dennis9819/Z8C-Homebrew-Computer/Modules/001-CPU Board V1/Schematics.pdf

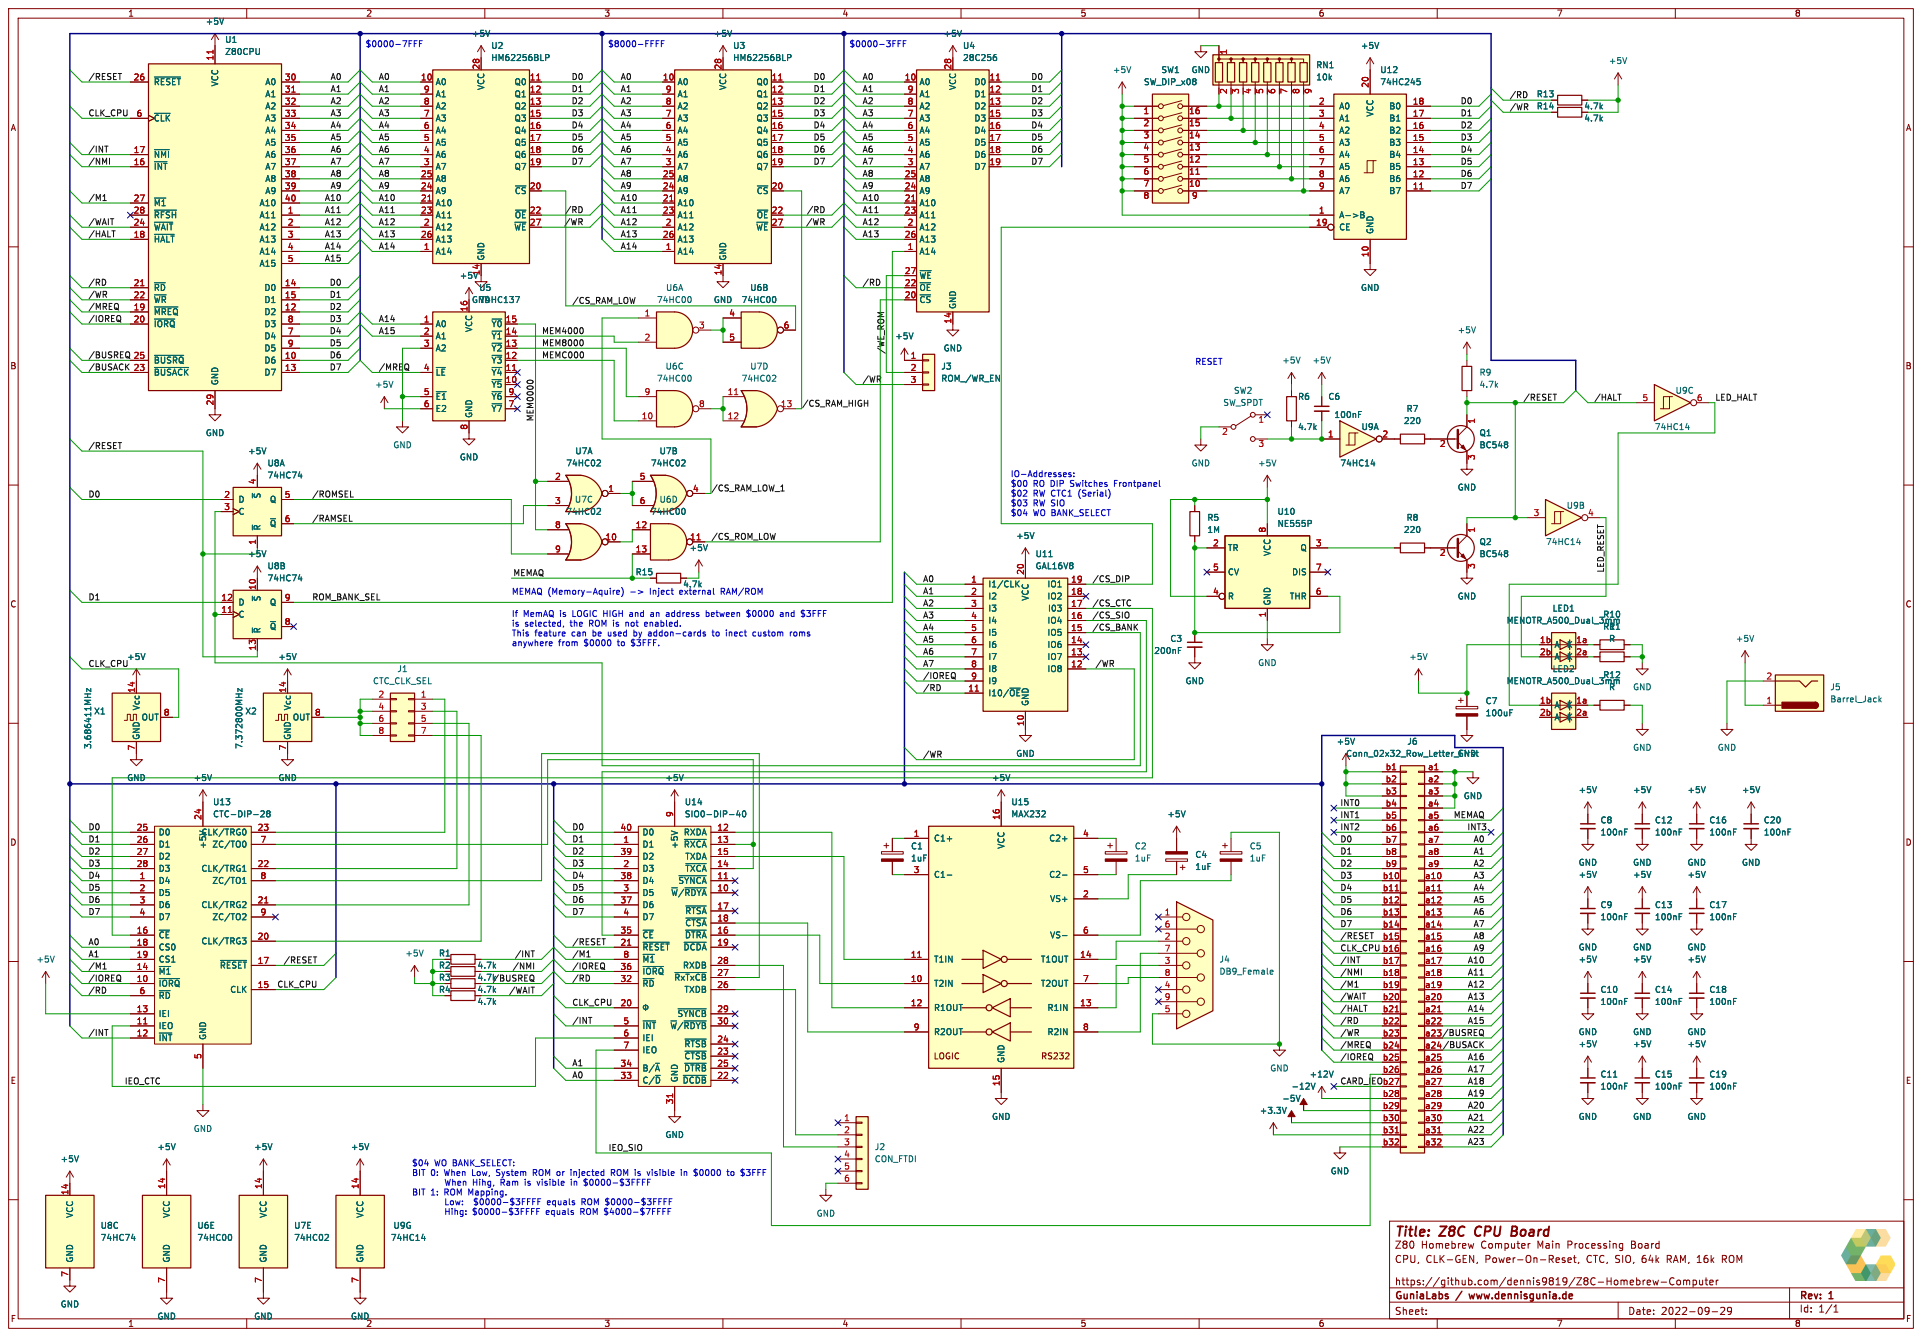
[picture p10: page 1]

IO-Addresses: $00 RO DIP Switches Frontpanel $02 RW CTC1 (Serial) $03 RW SIO
+5V U11 GAL16V8 GND 10 VCC 20

If MemAQ is LOGIC HIGH and an address between $0000 and $3FFF

5 ~{RD} 6 ZC/TO0 7 ZC/TO1 8 ZC/TO2 9 GND +5V

5 ~{RD} 6 ZC/TO0 7 ZC/TO1 8 ZC/TO2 9 U13 CTC-DIP-28 GND

Id: 1/1 Title: Z8C CPU Board

https://github.com/dennis9819/Z8C-Homebrew-Computer
