dennis9819/Z8C-Homebrew-Computer/Modules/002-MIO Board V1/Schematics_Rev2.pdf

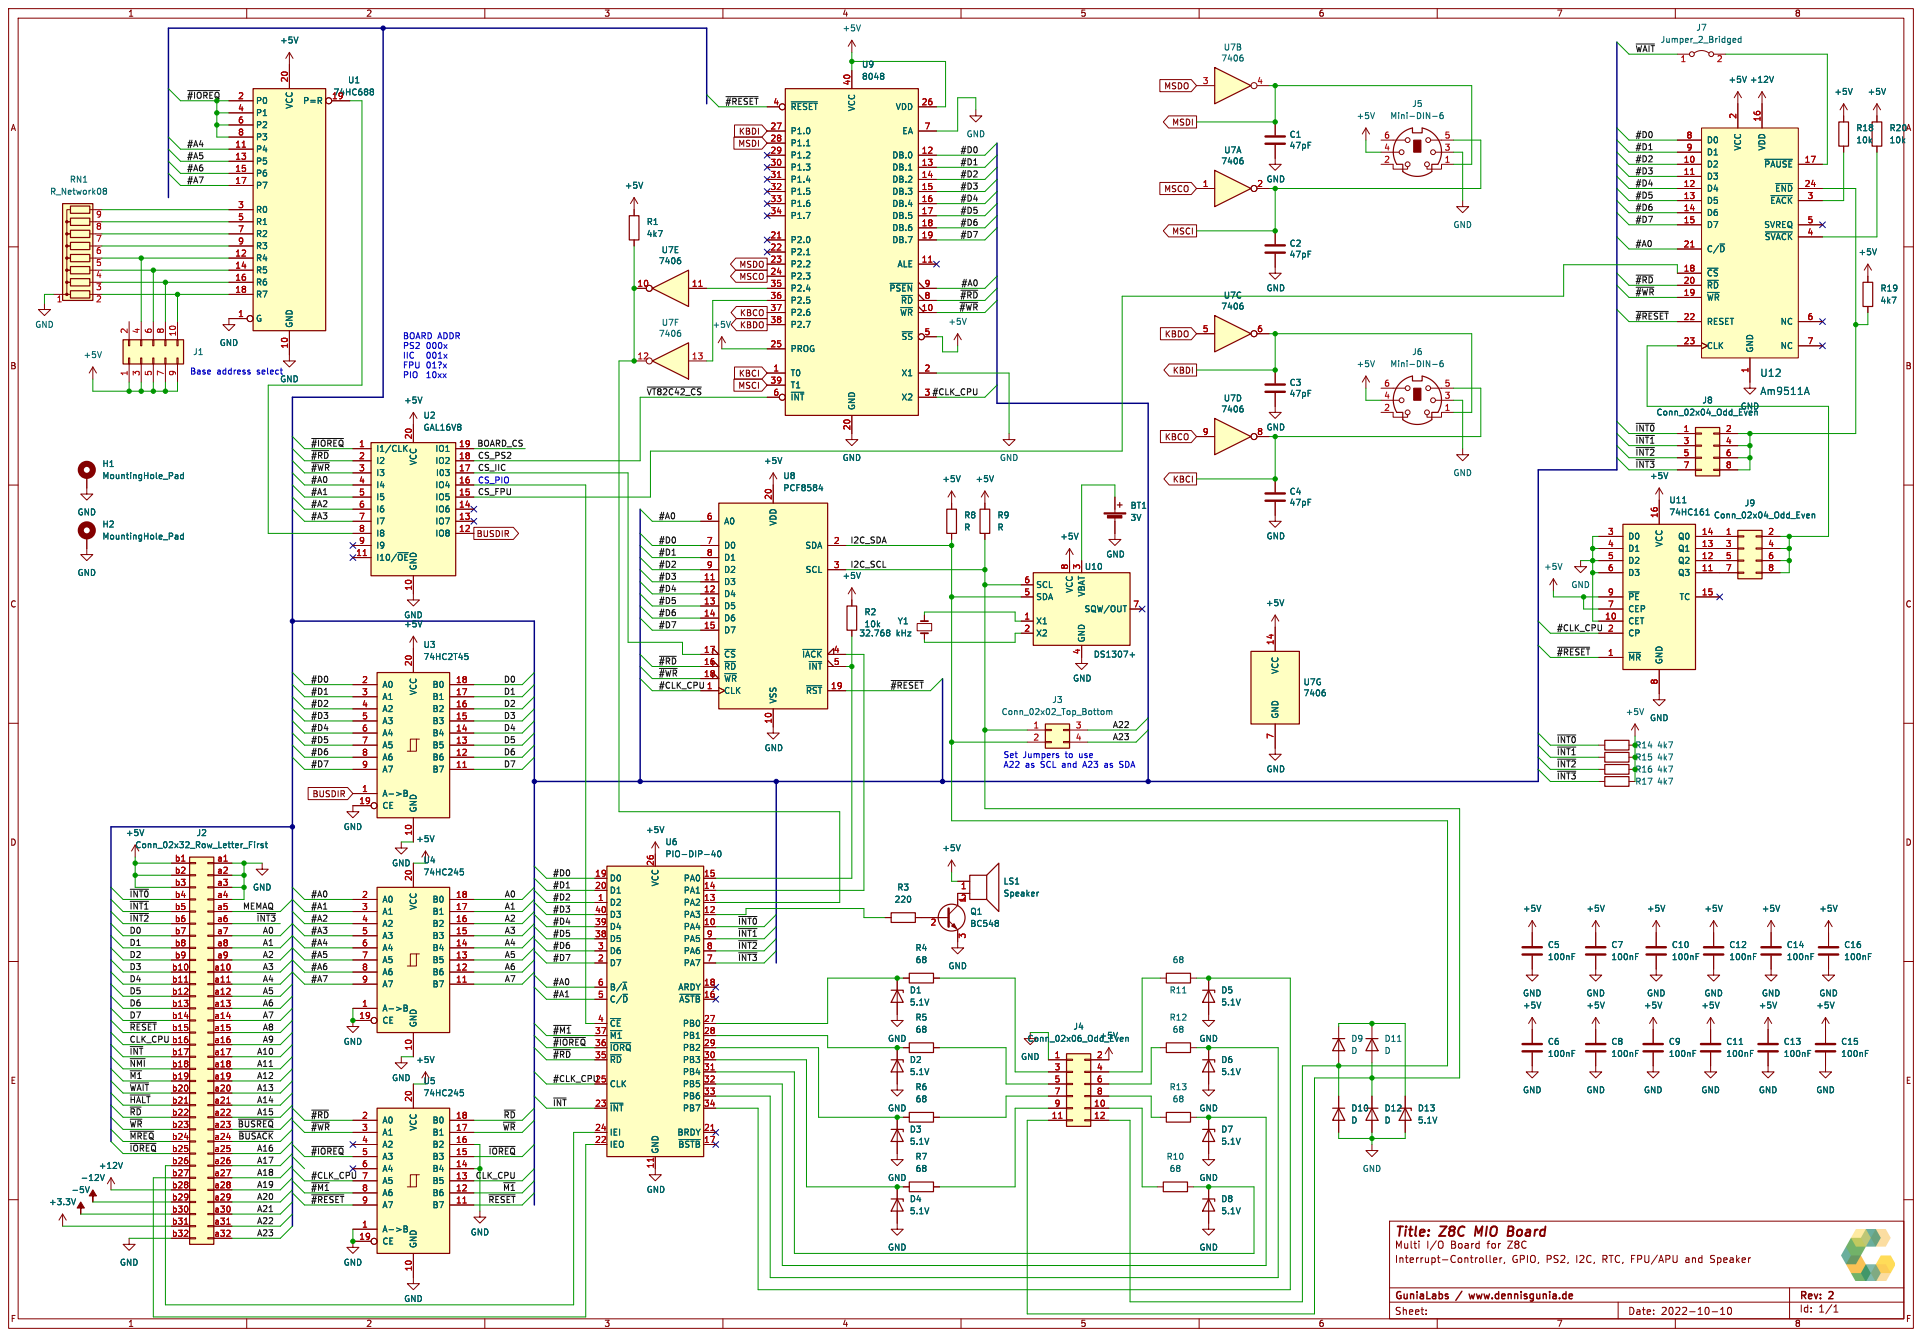
[picture p11: page 1]

4 SDA 5 SCL 6 SQW/OUT 7 VCC

Id: 1/1 Title: Z8C MIO Board
