dennis9819/Z8C-Homebrew-Computer/.old/Schematics/Z80-SID/Z80-SID.kicad_pcb

## KiCad design .old/Schematics/Z80-SID/Z80-SID.kicad_pcb (2022-10-24, an earlier design)

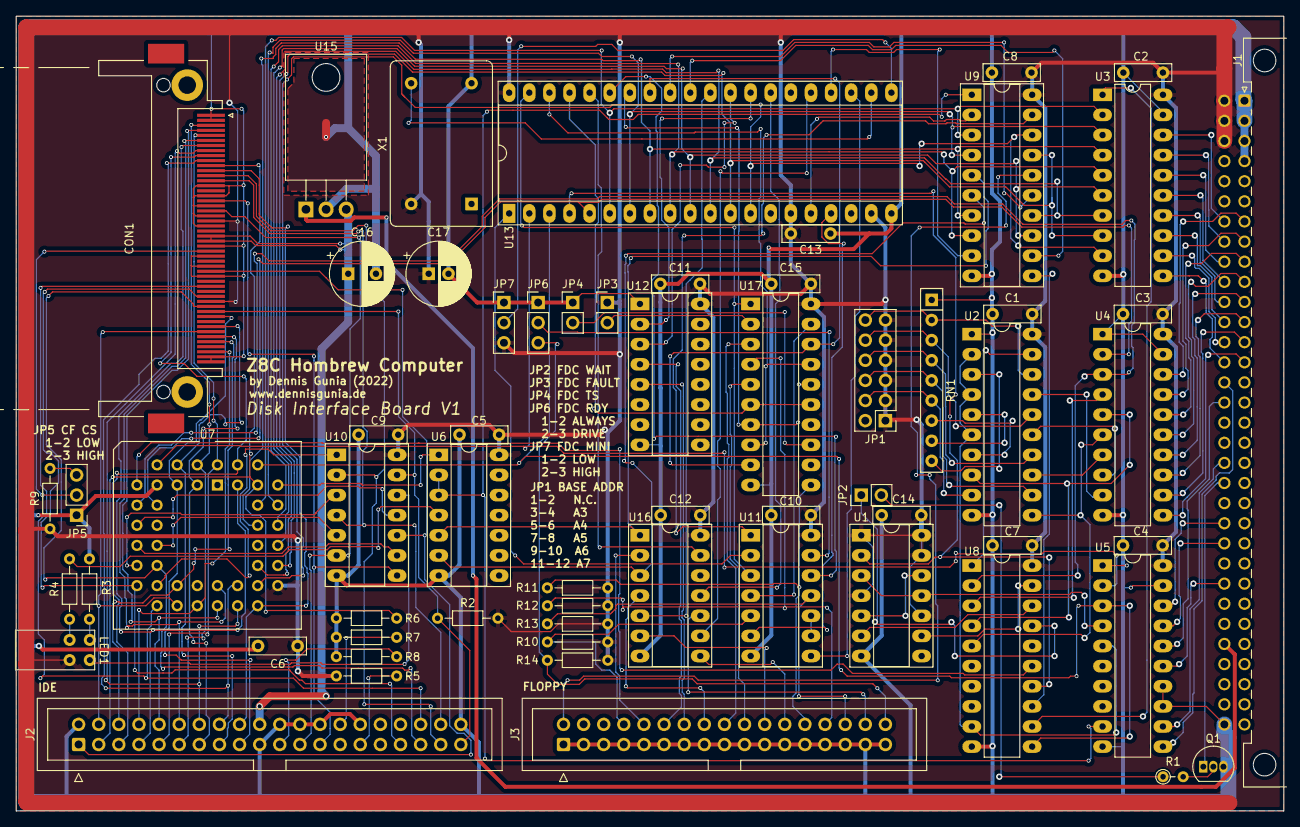
[picture p26: board Z80-SID.kicad_pcb from above]

Board: 2 copper layers, 160.0 x 100.3 mm, 62 parts (0 on the bottom side), 151 nets.

Parts:
C1, C2, C3, C4, C5, C6, C7, C8, C9, C10, C11, C12, C13, C14, C15: 100nF; C_Rect_L7.0mm_W2.0mm_P5.00mm
C16: 470uF; CP_Radial_D8.0mm_P3.50mm
C17: 100uF; CP_Radial_D8.0mm_P2.50mm
CON1: CF-CARD; CF-Card_3M_N7E50-E516xx-30
J1: Conn_02x32_Row_Letter_First; DIN41612_Q_2x32_Male_Horizontal_THT
J2: IDE Connector; IDC-Header_2x20_P2.54mm_Vertical
J3: Floppy Connector; IDC-Header_2x17_P2.54mm_Vertical
JP1: Conn_02x06_Odd_Even; PinHeader_2x06_P2.54mm_Vertical
JP2, JP3, JP4: Jumper_2_Bridged; PinHeader_1x02_P2.54mm_Vertical
JP5, JP6, JP7: Jumper_3_Open; PinHeader_1x03_P2.54mm_Vertical
LED1: MENOTR_A500_Dual_3mm; MENTOR A500 Dual 3mm
Q1: BC548; TO-92_Inline
R1: 220; R_Axial_DIN0204_L3.6mm_D1.6mm_P2.54mm_Vertical
R2, R3, R4, R5, R6, R7, R8, R9, R10, R11, R12, R13, R14: 10k; R_Axial_DIN0204_L3.6mm_D1.6mm_P7.62mm_Horizontal
RN1: R_Network08; R_Array_SIP9
U1: 74HC74; DIP-14_W7.62mm_Socket_LongPads
U2: 74LS688; DIP-20_W7.62mm_LongPads
U3, U4, U5: 74HC245; DIP-20_W7.62mm_LongPads
U6: 74HC02; DIP-14_W7.62mm_Socket_LongPads
U7: 82C55A_PLCC; PLCC-44_THT-Socket
U8: GAL16V8; DIP-20_W7.62mm_LongPads
U9: 74HCT273; DIP-20_W7.62mm_Socket_LongPads
U10, U16: 74HCT04; DIP-14_W7.62mm_Socket_LongPads
U11: 74HC14; DIP-14_W7.62mm_Socket_LongPads
U12: 74HCT139; DIP-16_W7.62mm_Socket_LongPads
U13: FDC9266; DIP-40_W15.24mm_Socket_LongPads
U15: L7805; TO-220-3_Horizontal_TabDown
U17: 74HC240; DIP-20_W7.62mm_LongPads
X1: 8MHz; Oscillator_DIP-14

Connections:
+5V: C1.1, C2.1, C3.1, C4.1, C5.1, C6.1, C7.1, C8.1, C9.1, C10.1, C11.1, C12.1, C13.1, C14.1, C15.1, C17.1, CON1.36 (/WE), CON1.44 (/REG), J1.b1, J1.b2, J1.b3, JP1.1, JP1.3, JP1.5, JP1.7, JP1.9, JP1.11, JP3.1 (A), JP7.3 (B), LED1.2b (A), R2.2, R5.1, R9.1, R10.2, R11.2, R12.2, R13.2, R14.2, U1.1 (~R), U1.4 (~S), U1.10 (~S), U1.13 (~R), U1.14 (VCC), U2.20 (VCC), U3.20 (VCC), U4.20 (VCC), U5.20 (VCC), U6.14 (VCC), U7.29 (VCC), U8.20 (VCC), U9.20 (VCC), U10.14 (VCC), U11.14 (VCC), U12.16 (VCC), U13.15 (~DACK), U13.19 (TEST), U13.40 (VCC), U16.14 (VCC), U17.20 (VCC), X1.14 (Vcc)
+12V: J1.b28, U15.1 (IN)
/#A0: U4.2 (A0), U7.10 (A0), U13.5 (A0)
/#A1: U4.3 (A1), U7.9 (A1), U8.2 (I2)
/#A2: U4.4 (A2), U8.3 (I3)
/#A3: U2.8 (P3), U4.5 (A3), U8.4 (I4)
/#A4: U2.11 (P4), U4.6 (A4), U8.5 (I5)
/#A5: U2.13 (P5), U4.7 (A5)
/#A6: U2.15 (P6), U4.8 (A6)
/#A7: U2.17 (P7), U4.9 (A7)
/#CLK_CPU: U1.3 (C), U1.11 (C), U5.4 (A2)
/#D0: U3.2 (A0), U7.38 (D0), U9.3 (D0), U13.6 (DB0)
/#D1: U3.3 (A1), U7.37 (D1), U9.4 (D1), U13.7 (DB1)
/#D2: U3.4 (A2), U7.36 (D2), U9.7 (D2), U13.8 (DB2)
/#D3: U3.5 (A3), U7.35 (D3), U9.8 (D3), U13.9 (DB3)
/#D4: U3.6 (A4), U7.33 (D4), U9.13 (D4), U13.10 (DB4)
/#D5: U3.7 (A5), U7.32 (D5), U9.14 (D5), U13.11 (DB5)
/#D6: U3.8 (A6), U7.31 (D6), U9.17 (D6), U13.12 (DB6)
/#D7: U3.9 (A7), U7.30 (D7), U9.18 (D7), U13.13 (DB7)
/#RESET: U6.1, U7.39 (RESET)
/A0: J1.a7, U4.18 (B0)
/A1: J1.a8, U4.17 (B1)
/A2: J1.a9, U4.16 (B2)
/A3: J1.a10, U4.15 (B3)
/A4: J1.a11, U4.14 (B4)
/A5: J1.a12, U4.13 (B5)
/A6: J1.a13, U4.12 (B6)
/A7: J1.a14, U4.11 (B7)
/CLK_CPU: J1.b16, U5.16 (B2)
/CSEL: J2.28, R7.2
/D0: J1.b7, U3.18 (B0)
/D1: J1.b8, U3.17 (B1)
/D2: J1.b9, U3.16 (B2)
/D3: J1.b10, U3.15 (B3)
/D4: J1.b11, U3.14 (B4)
/D5: J1.b12, U3.13 (B5)
/D6: J1.b13, U3.12 (B6)
/D7: J1.b14, U3.11 (B7)
/DMACK: J2.29, R5.2
/DMARQ: J2.21, R8.2
/IDE_VCC: C16.1, CON1.13 (VCC2), CON1.38 (VCC1), J2.20, U15.3 (OUT)
/PA0: CON1.21 (D0), J2.17, U7.5 (PA0)
/PA1: CON1.22 (D1), J2.15, U7.4 (PA1)
/PA2: CON1.23 (D2), J2.13, U7.3 (PA2)
/PA3: CON1.2 (D3), J2.11, U7.2 (PA3)
/PA4: CON1.3 (D4), J2.9, U7.44 (PA4)
/PA5: CON1.4 (D5), J2.7, U7.43 (PA5)
/PA6: CON1.5 (D6), J2.5, U7.42 (PA6)
/PA7: CON1.6 (D7), J2.3, R6.2, U7.41 (PA7)
/PB0: CON1.47 (D8), J2.4, U7.20 (PB0)
/PB1: CON1.48 (D9), J2.6, U7.21 (PB1)
/PB2: CON1.49 (D10), J2.8, U7.22 (PB2)
/PB3: CON1.27 (D11), J2.10, U7.24 (PB3)
/PB4: CON1.28 (D12), J2.12, U7.25 (PB4)
/PB5: CON1.29 (D13), J2.14, U7.26 (PB5)
/PB6: CON1.30 (D14), J2.16, U7.27 (PB6)
/PB7: CON1.31 (D15), J2.18, U7.28 (PB7)
/PC0: CON1.20 (A0), J2.35, U7.16 (PC0)
/PC1: CON1.19 (A1), J2.33, U7.17 (PC1)
/PC2: CON1.18 (A2), J2.36, U7.18 (PC2)
/PC3: U7.19 (PC3), U10.1
/PC4: U7.15 (PC4), U10.3
/PC5: U7.14 (PC5), U10.5
/PC6: U7.13 (PC6), U10.9
/PC7: U7.11 (PC7), U10.11
/~#IOREQ: U2.2 (P0), U2.4 (P1), U2.6 (P2), U5.5 (A3), U8.9 (I9)
/~#RD: U5.2 (A0), U7.6 (~RD), U13.2 (~RD)
/~#RESET: U5.9 (A7), U6.2, U6.3, U9.1 (~Mr)
/~#WR: U5.3 (A1), U7.40 (~WR), U8.11 (I10/~OE), U13.3 (~WR)
/~ACTIVE: CON1.45 (/DASP), J2.39, R2.1, U10.13
/~DCS0: CON1.7 (/CS0), J2.37, U10.2
/~DCS1: CON1.32 (/CS1), J2.38, U10.4
/~DIOR: CON1.34 (/IORD), J2.25, U10.8
/~DIOW: CON1.35 (/IOWR), J2.23, U10.6
/~DRESET: CON1.41 (/RESET), J2.1, U10.10
/~IOREQ: J1.b25, U5.15 (B3)
/~M1: J1.b19, U5.12 (B6)
/~RD: J1.b22, U5.18 (B0)
/~RESET: J1.b15, U5.11 (B7)
/~WAIT: J1.b20, Q1.1 (C)
/~WR: J1.b23, U5.17 (B1)
BUSDIR: U3.1 (A->B), U8.12 (IO8)
CS_FDC: U1.2 (D), U8.14 (IO6), U13.4 (~CS)
CS_IDE: U7.7 (~CS), U8.15 (IO5)
CS_LATCH: U8.13 (IO7), U9.11 (Cp)
FDC_FLT/TR0: U13.33 (FLT/TR0), U17.9 (2Y3), U17.18 (1Y0)
FDC_FR/STEP: U13.37 (FR/STEP), U17.6 (1A2), U17.15 (2A1)
FDC_HD: U13.27 (HD), U16.11
FDC_HDL: U13.36 (HDL), U16.13
FDC_INDEX: U11.6, U13.17 (IDX)
FDC_LCT/DIR: U13.38 (LCT/DIR), U17.8 (1A3), U17.17 (2A0)
FDC_MINI: JP7.2 (C), U13.21 (MINI)
FDC_P0: U9.15 (Q5), U13.32 (P2)
FDC_P1: U9.12 (Q4), U13.31 (P1)
FDC_P2: U9.9 (Q3), U13.24 (P0)
FDC_RDY: U11.12, U13.35 (RDY)
FDC_RESET: U11.2, U13.1 (RST)
FDC_RW/~SEEK: U11.4, U17.19 (2OE)
FDC_TC: U9.2 (Q0), U13.16 (TC)
FDC_US0: U12.3 (A1), U13.29 (US0)
FDC_US1: U12.2 (A0), U13.28 (US1)
FDC_WDOUT: U13.30 (WDOUT), U16.5
FDC_WE: U13.25 (WE), U16.9
FDC_WP/TS: U13.34 (WP/TS), U17.7 (2Y2), U17.16 (1Y1)
FDC_~DSKD: U11.8, U13.23 (~DSKD)
FDC_~FAULT: JP3.2 (B), U17.2 (1A0)
FDC_~RDY: JP6.2 (C), U11.13
FDC_~RW/SEEK: U11.3, U13.39 (~RW/SEEK), U17.1 (1OE)
FDC_~TS: JP4.2 (B), U17.13 (2A2)
FD_DENSEEL: J3.2, U9.16 (Q6)
FD_MOTEA: U6.5, U9.5 (Q1), U16.1
FD_MOTEB: U6.6, U9.6 (Q2), U16.3
FD_~ACTIVITY: R4.2, U6.4
FD_~DC/RDY: J3.34, JP6.3 (B), R14.1
FD_~DIR: J3.18, U17.3 (2Y0)
FD_~INDEX: J3.8, R10.1, U11.5
FD_~MOTEA: J3.10, U16.2
FD_~MOTEB: J3.16, U16.4
FD_~RDATA: J3.30, R13.1, U11.11
FD_~SIDE: J3.32, U16.10
FD_~STEP: J3.20, U17.5 (2Y1)
FD_~TRK0: J3.26, R11.1, U17.11 (2A3)
FD_~WDATA: J3.22, U16.6
FD_~WGATE: J3.24, U16.8
FD_~WRTPRO: J3.28, R12.1, U17.4 (1A1)
GND: C1.2, C2.2, C3.2, C4.2, C5.2, C6.2, C7.2, C8.2, C9.2, C10.2, C11.2, C12.2, C13.2, C14.2, C15.2, C16.2, C17.2, CON1.1 (GND1), CON1.8 (A10), CON1.9 (/ATASEL), CON1.10 (A9), CON1.11 (A8), CON1.12 (A7), CON1.14 (A6), CON1.15 (A5), CON1.16 (A4), CON1.17 (A3), CON1.25 (/CD2), CON1.26 (/CD1), CON1.50 (GND2), J1.a1, J1.a2, J1.a3, J1.a4, J1.b32, J2.2, J2.19, J2.22, J2.24, J2.26, J2.30, J2.40, J3.1, J3.3, J3.5, J3.7, J3.9, J3.11, J3.13, J3.15, J3.17, J3.19, J3.21, J3.23, J3.25, J3.27, J3.29, J3.31, J3.33, JP4.1 (A), JP5.1 (A), JP6.1 (A), JP7.1 (A), Q1.3 (E), R3.2, R6.1, R7.1, R8.1, RN1.1 (common), U1.7 (GND), U2.1 (G), U2.10 (GND), U3.10 (GND), U3.19 (CE), U4.1 (A->B), U4.10 (GND), U4.19 (CE), U5.1 (A->B), U5.10 (GND), U5.13 (B5), U5.14 (B4), U5.19 (CE), U6.7 (GND), U7.8 (GND), U8.10 (GND), U9.10 (GND), U10.7 (GND), U11.7 (GND), U12.1 (E), U12.8 (GND), U13.20 (GND), U15.2 (GND), U16.7 (GND), U17.10 (GND), X1.7 (GND)
unnamed: CON1.39 (/CSEL), JP5.2 (C)
unnamed: JP1.4, RN1.6 (R5), U2.9 (R3)
unnamed: JP1.6, RN1.5 (R4), U2.12 (R4)
unnamed: JP1.8, RN1.4 (R3), U2.14 (R5)
unnamed: JP1.10, RN1.3 (R2), U2.16 (R6)
unnamed: JP1.12, RN1.2 (R1), U2.18 (R7)
unnamed: JP2.1 (A), U8.17 (I03)
unnamed: JP2.2 (B), R1.1
unnamed: JP5.3 (B), R9.2
unnamed: LED1.1a (K), R3.1
unnamed: LED1.1b (A), U10.12
unnamed: LED1.2a (K), R4.1
unnamed: Q1.2 (B), R1.2
unnamed: RN1.7 (R6), U2.7 (R2)
unnamed: RN1.8 (R7), U2.5 (R1)
unnamed: RN1.9 (R8), U2.3 (R0)
unnamed: U1.6 (~Q), U8.18 (IO2)
unnamed: U1.9 (Q), U8.19 (IO1)
unnamed: U1.5 (Q), U1.12 (D)
unnamed: U2.19 (P=R), U8.1 (I1/CLK)
unnamed: U9.19 (Q7), U11.1
unnamed: U11.9, U11.10
unnamed: U13.22 (CLK), X1.8 (OUT)
~FD_DSA1: J3.12, U12.4 (O0)
~FD_DSB1: J3.14, U12.5 (O1)
