dennis9819/Z8C-Homebrew-Computer/.old/Schematics/Z80-MIDI/z80-MIDI.kicad_pcb

## KiCad design .old/Schematics/Z80-MIDI/z80-MIDI.kicad_pcb (2022-11-02, an earlier design)

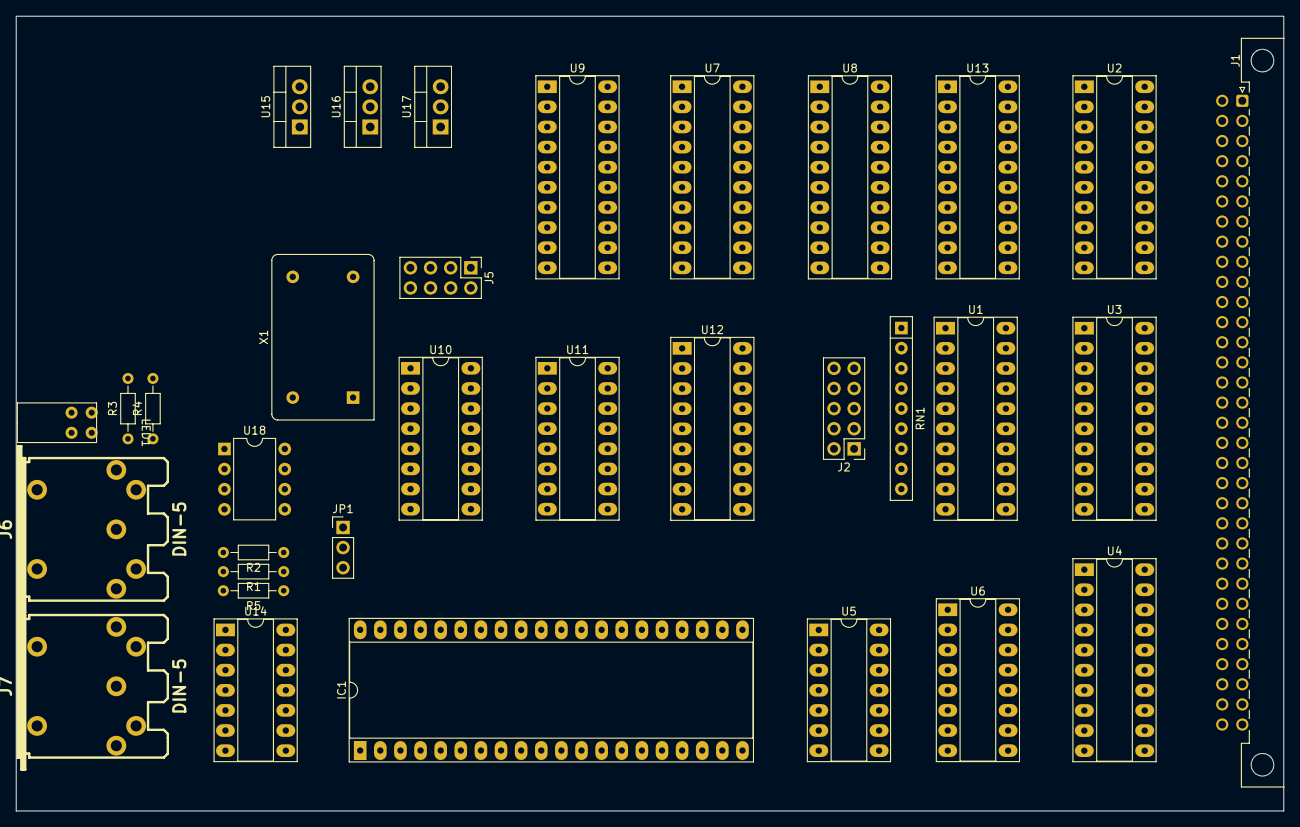
[picture p27: board z80-MIDI.kicad_pcb from above]

Board: 2 copper layers, 160.0 x 100.3 mm, 33 parts (0 on the bottom side), 102 nets, no tracks yet.

Parts:
IC1: SIO0-DIP-40; DIP-40_W15.24mm_Socket_LongPads
J1: Conn_02x32_Row_Letter_First; DIN41612_Q_2x32_Male_Horizontal_THT
J2: Conn_02x05_Odd_Even; PinHeader_2x05_P2.54mm_Vertical
J5: Conn_02x04_Odd_Even; PinHeader_2x04_P2.54mm_Vertical
J6, J7: DIN-5; din-5
JP1: Jumper_3_Open; PinHeader_1x03_P2.54mm_Vertical
LED1: MENOTR_A500_Dual_3mm; MENTOR A500 Dual 3mm
R1, R2, R3, R4, R5: 10k; R_Axial_DIN0204_L3.6mm_D1.6mm_P7.62mm_Horizontal
RN1: R_Network08; R_Array_SIP9
U1: 74LS688; DIP-20_W7.62mm_Socket_LongPads
U2, U3, U4, U13: 74HC245; DIP-20_W7.62mm_Socket_LongPads
U5: 74HC02; DIP-14_W7.62mm_Socket_LongPads
U6: 74HC138; DIP-16_W7.62mm_Socket_LongPads
U7, U8, U9: 74LS573; DIP-20_W7.62mm_Socket_LongPads
U10: 74LS590; DIP-16_W7.62mm_Socket_LongPads
U11: 74HCT4051; DIP-16_W7.62mm_Socket_LongPads
U12: AD570; DIP-18_W7.62mm_Socket_LongPads
U14: 74LS06; DIP-14_W7.62mm_Socket_LongPads
U15: LM7915_TO220; TO-220-3_Vertical
U16: LM7810_TO220; TO-220-3_Vertical
U17: LM7910_TO220; TO-220-3_Vertical
U18: 6N137; DIP-8_W7.62mm
X1: 1MHz; Oscillator_DIP-14

Connections:
+5V: IC1.9 (+5V), J1.b1, J1.b2, J1.b3, J2.1, J2.3, J2.5, J2.7, J2.9, R1.1, R3.2, R4.2, R5.1, U1.20 (VCC), U2.20 (VCC), U3.20 (VCC), U4.20 (VCC), U5.14 (VCC), U6.16 (VCC), U7.20 (VCC), U8.20 (VCC), U9.20 (VCC), U10.10 (~MRC), U10.16 (VCC), U12.10 (VCC), U13.1 (A->B), U13.20 (VCC), U14.14 (VCC), U18.7 (EN), U18.8 (VCC), X1.14 (Vcc)
/#A0: IC1.34 (B/~A), U3.2 (A0), U6.1 (A0)
/#A1: IC1.33 (C/~D), U3.3 (A1), U6.2 (A1)
/#A2: U3.4 (A2), U5.8, U6.6 (E3)
/#A3: U1.8 (P3), U3.5 (A3)
/#A4: U1.11 (P4), U3.6 (A4)
/#A5: U1.13 (P5), U3.7 (A5)
/#A6: U1.15 (P6), U3.8 (A6)
/#A7: U1.17 (P7), U3.9 (A7)
/#CLK_CPU: IC1.20 (Φ), U4.4 (A2)
/#D0: IC1.40 (D0), U2.2 (A0), U7.19 (Q0), U8.2 (D0), U9.19 (Q0), U13.18 (B0)
/#D1: IC1.1 (D1), U2.3 (A1), U7.18 (Q1), U8.3 (D1), U9.18 (Q1), U13.17 (B1)
/#D2: IC1.39 (D2), U2.4 (A2), U7.17 (Q2), U8.4 (D2), U9.17 (Q2), U13.16 (B2)
/#D3: IC1.2 (D3), U2.5 (A3), U7.16 (Q3), U8.5 (D3), U9.16 (Q3), U13.15 (B3)
/#D4: IC1.38 (D4), U2.6 (A4), U7.15 (Q4), U8.6 (D4), U9.15 (Q4), U13.14 (B4)
/#D5: IC1.3 (D5), U2.7 (A5), U7.14 (Q5), U8.7 (D5), U9.14 (Q5), U13.13 (B5)
/#D6: IC1.37 (D6), U2.8 (A6), U7.13 (Q6), U8.8 (D6), U9.13 (Q6), U13.12 (B6)
/#D7: IC1.4 (D7), U2.9 (A7), U7.12 (Q7), U8.9 (D7), U9.12 (Q7), U13.11 (B7)
/A0: J1.a7, U3.18 (B0)
/A1: J1.a8, U3.17 (B1)
/A2: J1.a9, U3.16 (B2)
/A3: J1.a10, U3.15 (B3)
/A4: J1.a11, U3.14 (B4)
/A5: J1.a12, U3.13 (B5)
/A6: J1.a13, U3.12 (B6)
/A7: J1.a14, U3.11 (B7)
/CLK_CPU: J1.b16, U4.16 (B2)
/D0: J1.b7, U2.18 (B0)
/D1: J1.b8, U2.17 (B1)
/D2: J1.b9, U2.16 (B2)
/D3: J1.b10, U2.15 (B3)
/D4: J1.b11, U2.14 (B4)
/D5: J1.b12, U2.13 (B5)
/D6: J1.b13, U2.12 (B6)
/D7: J1.b14, U2.11 (B7)
//IOREQ: U1.2 (P0), U1.4 (P1), U1.6 (P2)
/~#IOREQ: IC1.36 (~IORQ), U4.5 (A3)
/~#M1: IC1.8 (~M1), U4.8 (A6)
/~#RD: IC1.32 (~RD), U4.2 (A0), U5.2, U6.3 (A2)
/~#RESET: IC1.21 (~RESET), U4.9 (A7)
/~INT: IC1.5 (~INT), J1.b17
/~IOREQ: J1.b25, U4.15 (B3)
/~M1: J1.b19, U4.12 (B6)
/~RD: J1.b22, U4.18 (B0)
/~RESET: J1.b15, U4.11 (B7)
/~WR: J1.b23, U4.17 (B1)
ADC_START: U8.16 (Q3), U12.11 (BLNK/~CONV)
BUF_POTAX: J5.1, U9.8 (D6)
BUF_POTAY: J5.3, U9.9 (D7)
BUF_POTBX: J5.5, U7.8 (D6)
BUF_POTBY: J5.7, U7.9 (D7)
DEC_BUF_DIR: U2.1 (A->B), U5.1
GND: IC1.31 (GND), J1.a1, J1.a2, J1.a3, J1.a4, J1.b32, J7.3, RN1.1 (common), U1.1 (G), U1.10 (GND), U2.10 (GND), U2.19 (CE), U3.1 (A->B), U3.10 (GND), U3.19 (CE), U4.1 (A->B), U4.10 (GND), U4.13 (B5), U4.14 (B4), U4.19 (CE), U5.7 (GND), U6.8 (GND), U7.10 (GND), U8.1 (OE), U8.10 (GND), U9.10 (GND), U10.8 (GND), U10.12 (~CE), U10.14 (~OE), U11.6 (~E), U11.8 (GND), U12.14 (ANALOG_COM), U12.15 (BIPOLAR), U12.16 (DIGITAL_COM), U13.10 (GND), U14.7 (GND), U18.5 (GND), X1.7 (GND)
MIDI_IN: IC1.12 (RXDA), JP1.1 (A), U14.5, U14.10
MIDI_OUT: IC1.15 (TXDA), JP1.3 (B), U14.9
MUX_0: U8.19 (Q0), U11.11 (S0)
MUX_1: U8.18 (Q1), U11.10 (S1)
MUX_2: U8.17 (Q2), U11.9 (S2)
unnamed: IC1.13 (~RXCA), IC1.14 (~TXCA), IC1.27 (~RxTxCB), U10.4 (Q4)
unnamed: J2.2, RN1.6 (R5), U1.9 (R3)
unnamed: J2.4, RN1.5 (R4), U1.12 (R4)
unnamed: J2.6, RN1.4 (R3), U1.14 (R5)
unnamed: J2.8, RN1.3 (R2), U1.16 (R6)
unnamed: J2.10, RN1.2 (R1), U1.18 (R7)
unnamed: J6.2, U18.3 (C)
unnamed: J6.4, U18.2 (A)
unnamed: J7.2, R2.2
unnamed: J7.4, R5.2
unnamed: JP1.2 (C), U14.3
unnamed: LED1.1a (K), U14.8
unnamed: LED1.1b (A), R3.1
unnamed: LED1.2a (K), U14.6
unnamed: LED1.2b (A), R4.1
unnamed: R1.2, U14.11, U18.6 (VO)
unnamed: R2.1, U14.2
unnamed: RN1.7 (R6), U1.7 (R2)
unnamed: RN1.8 (R7), U1.5 (R1)
unnamed: RN1.9 (R8), U1.3 (R0)
unnamed: U1.19 (P=R), U5.3, U5.9, U6.4 (E1), U6.5 (E2)
unnamed: U5.5, U5.6, U5.10
unnamed: U5.13, U8.11 (Load)
unnamed: U10.11 (CPC), U10.13 (CPR), X1.8 (OUT)
unnamed: U11.3 (A), U12.13 (ANALOG_IN)
unnamed: U12.2 (D7), U13.9 (A7)
unnamed: U12.3 (D6), U13.8 (A6)
unnamed: U12.4 (D5), U13.7 (A5)
unnamed: U12.5 (D4), U13.6 (A4)
unnamed: U12.6 (D3), U13.5 (A3)
unnamed: U12.7 (D2), U13.4 (A2)
unnamed: U12.8 (D1), U13.3 (A1)
unnamed: U12.9 (D0), U13.2 (A0)
unnamed: U14.1, U14.4
POTAX: J5.2, U11.13 (A0)
POTAY: J5.4, U11.14 (A1)
POTBX: J5.6, U11.15 (A2)
POTBY: J5.8, U11.12 (A3)
~ADC_RDY: U7.7 (D5), U9.7 (D5), U12.17 (~DATA_RDY)
~CS_SIO: IC1.35 (~CE), U5.4
~RD_ADC: U6.12 (O3), U13.19 (CE)
~RD_PORTA: U6.15 (O0), U9.1 (OE), U9.11 (Load)
~RD_PORTB: U6.14 (O1), U7.1 (OE), U7.11 (Load)
~WR_MUX: U5.11, U5.12, U6.9 (O6)
